norayr-noro/SUPPPAAAAAA_KEYBOARDDDD/SUPA_photos/bottomcase_(sketch).png

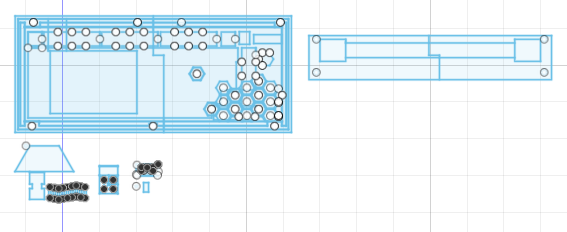
SUPA_photos/bottomcase_(sketch).png
