norayr-noro/SUPPPAAAAAA_KEYBOARDDDD/SUPA_photos/CAD_FULL.png

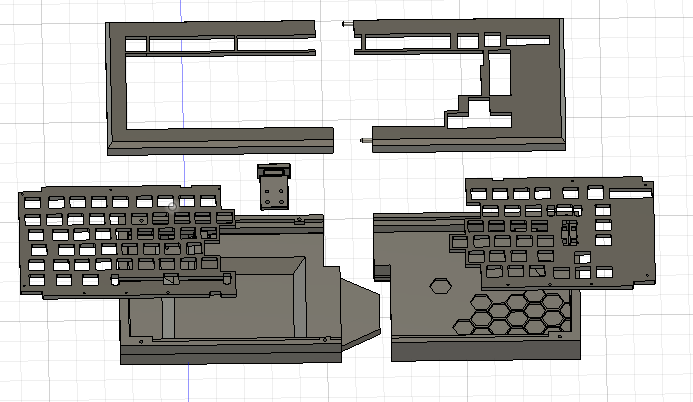
SUPA_photos/CAD_FULL.png
