norayr-noro/SUPPPAAAAAA_KEYBOARDDDD/SUPA_photos/PCB_full(diff.perc.).png

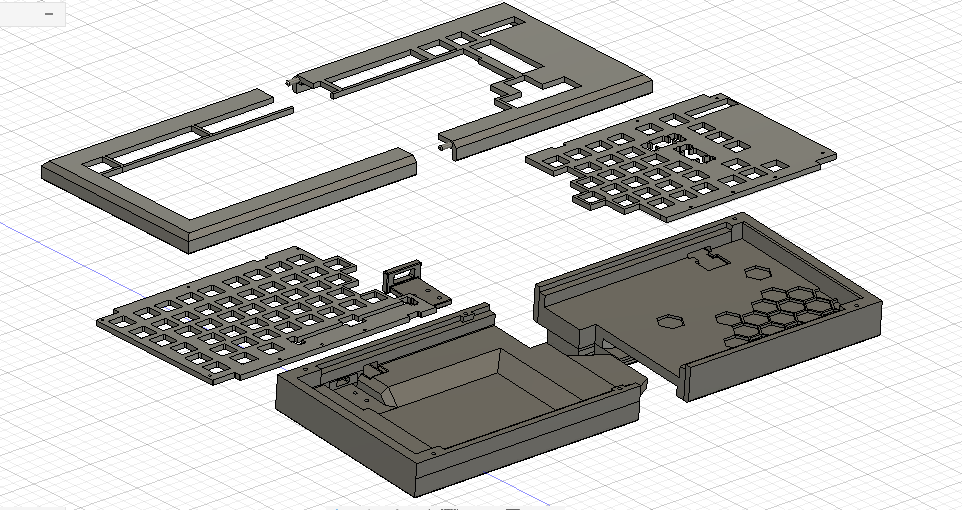
SUPA_photos/PCB_full(diff.perc.).png
