norayr-noro/SUPPPAAAAAA_KEYBOARDDDD/SUPA_photos/plate_(sketch).png

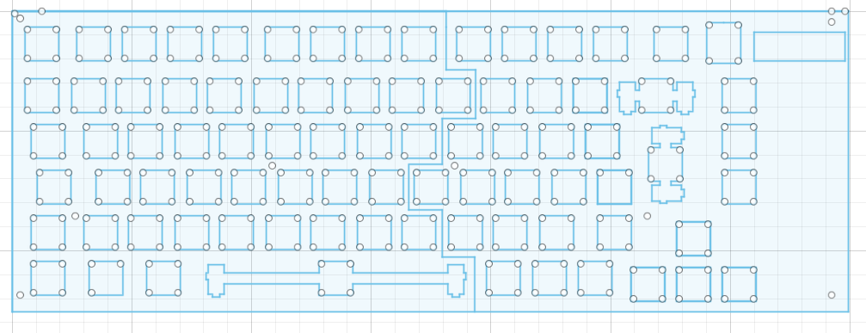
SUPA_photos/plate_(sketch).png
