norayr-noro/SUPPPAAAAAA_KEYBOARDDDD/SUPA_photos/Screenshot 2026-05-20 105105.png

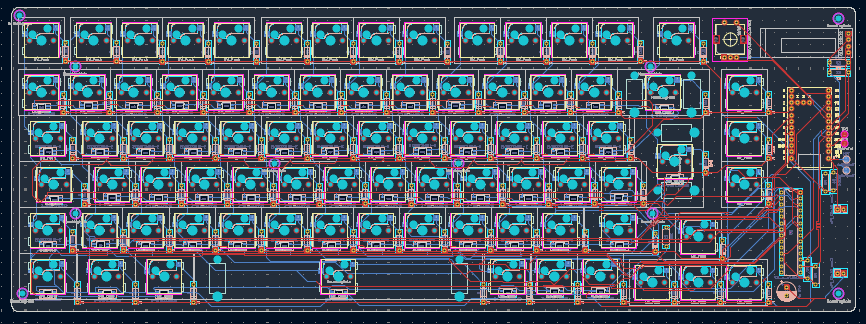
SUPA_photos/Screenshot 2026-05-20 105105.png
