norayr-noro/SUPPPAAAAAA_KEYBOARDDDD/SUPA_photos/Screenshot 2026-06-02 132246.png

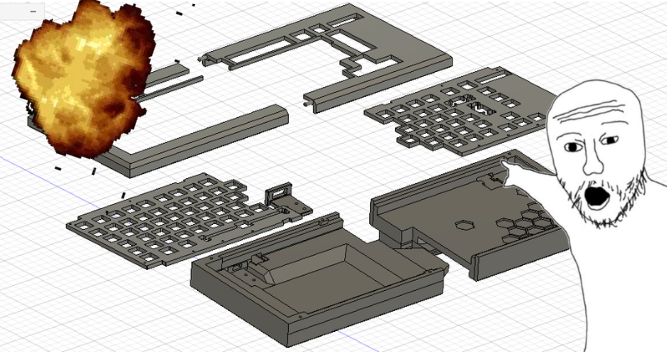
SUPA_photos/Screenshot 2026-06-02 132246.png
