norayr-noro/SUPPPAAAAAA_KEYBOARDDDD/SUPA_photos/topcase_(final).png

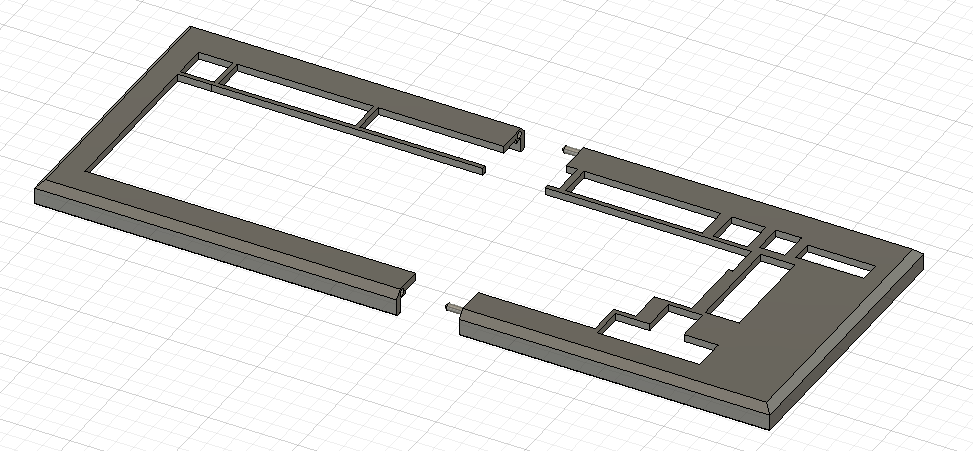
SUPA_photos/topcase_(final).png
