norayr-noro/SUPPPAAAAAA_KEYBOARDDDD/SUPA_photos/topcase_(sketch).png

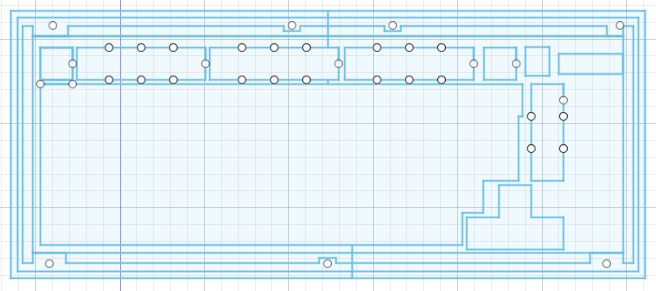
SUPA_photos/topcase_(sketch).png
