norayr-noro/SUPPPAAAAAA_KEYBOARDDDD/SUPA_photos/full_parts2.png

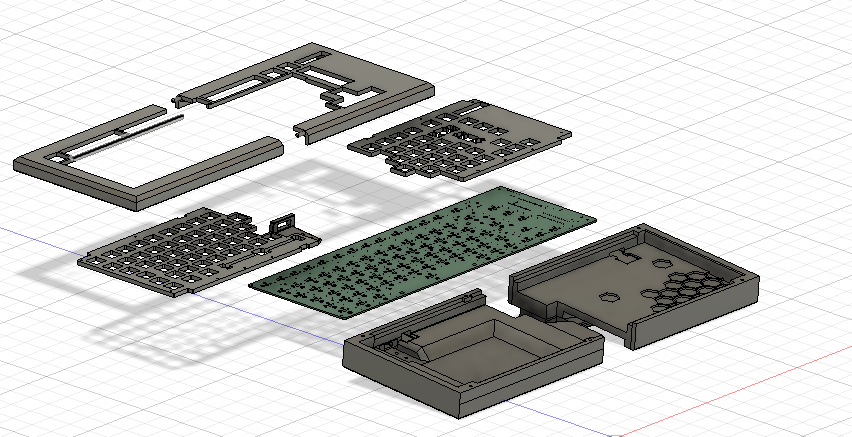
SUPA_photos/full_parts2.png
