norayr-noro/SUPPPAAAAAA_KEYBOARDDDD/SUPA_photos/full_parts.png

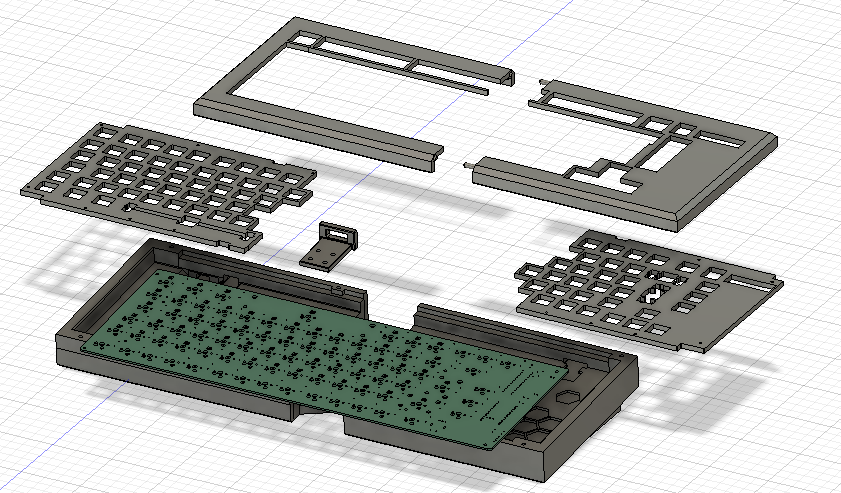
SUPA_photos/full_parts.png
