norayr-noro/SUPPPAAAAAA_KEYBOARDDDD/SUPA_photos/full_assembly2.png

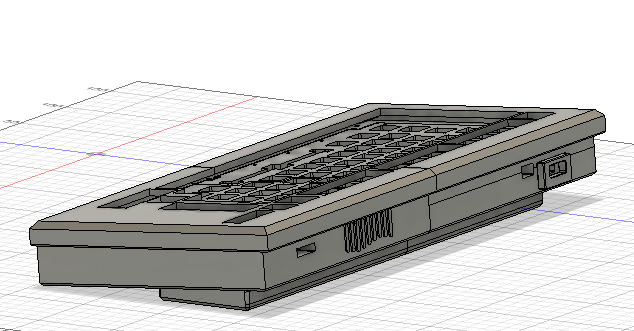
SUPA_photos/full_assembly2.png
