norayr-noro/SUPPPAAAAAA_KEYBOARDDDD/SUPA_photos/full_assembly.png

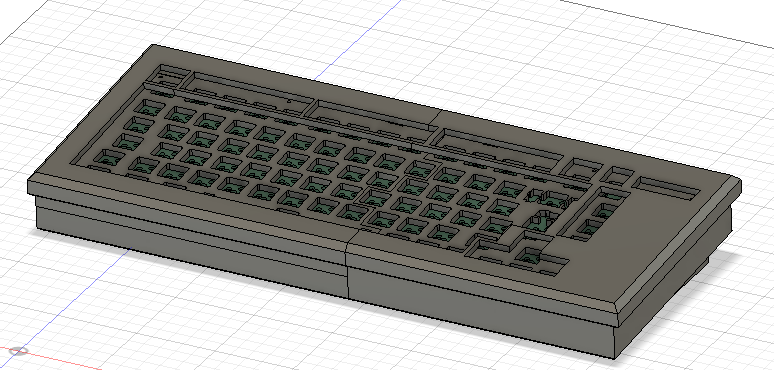
SUPA_photos/full_assembly.png
