norayr-noro/SUPPPAAAAAA_KEYBOARDDDD/SUPAAAA_KEYBOARD/SUPAAAA_KEYBOARD.kicad_sch

## KiCad design SUPAAAA_KEYBOARD/SUPAAAA_KEYBOARD.kicad_sch (2026-06-02)

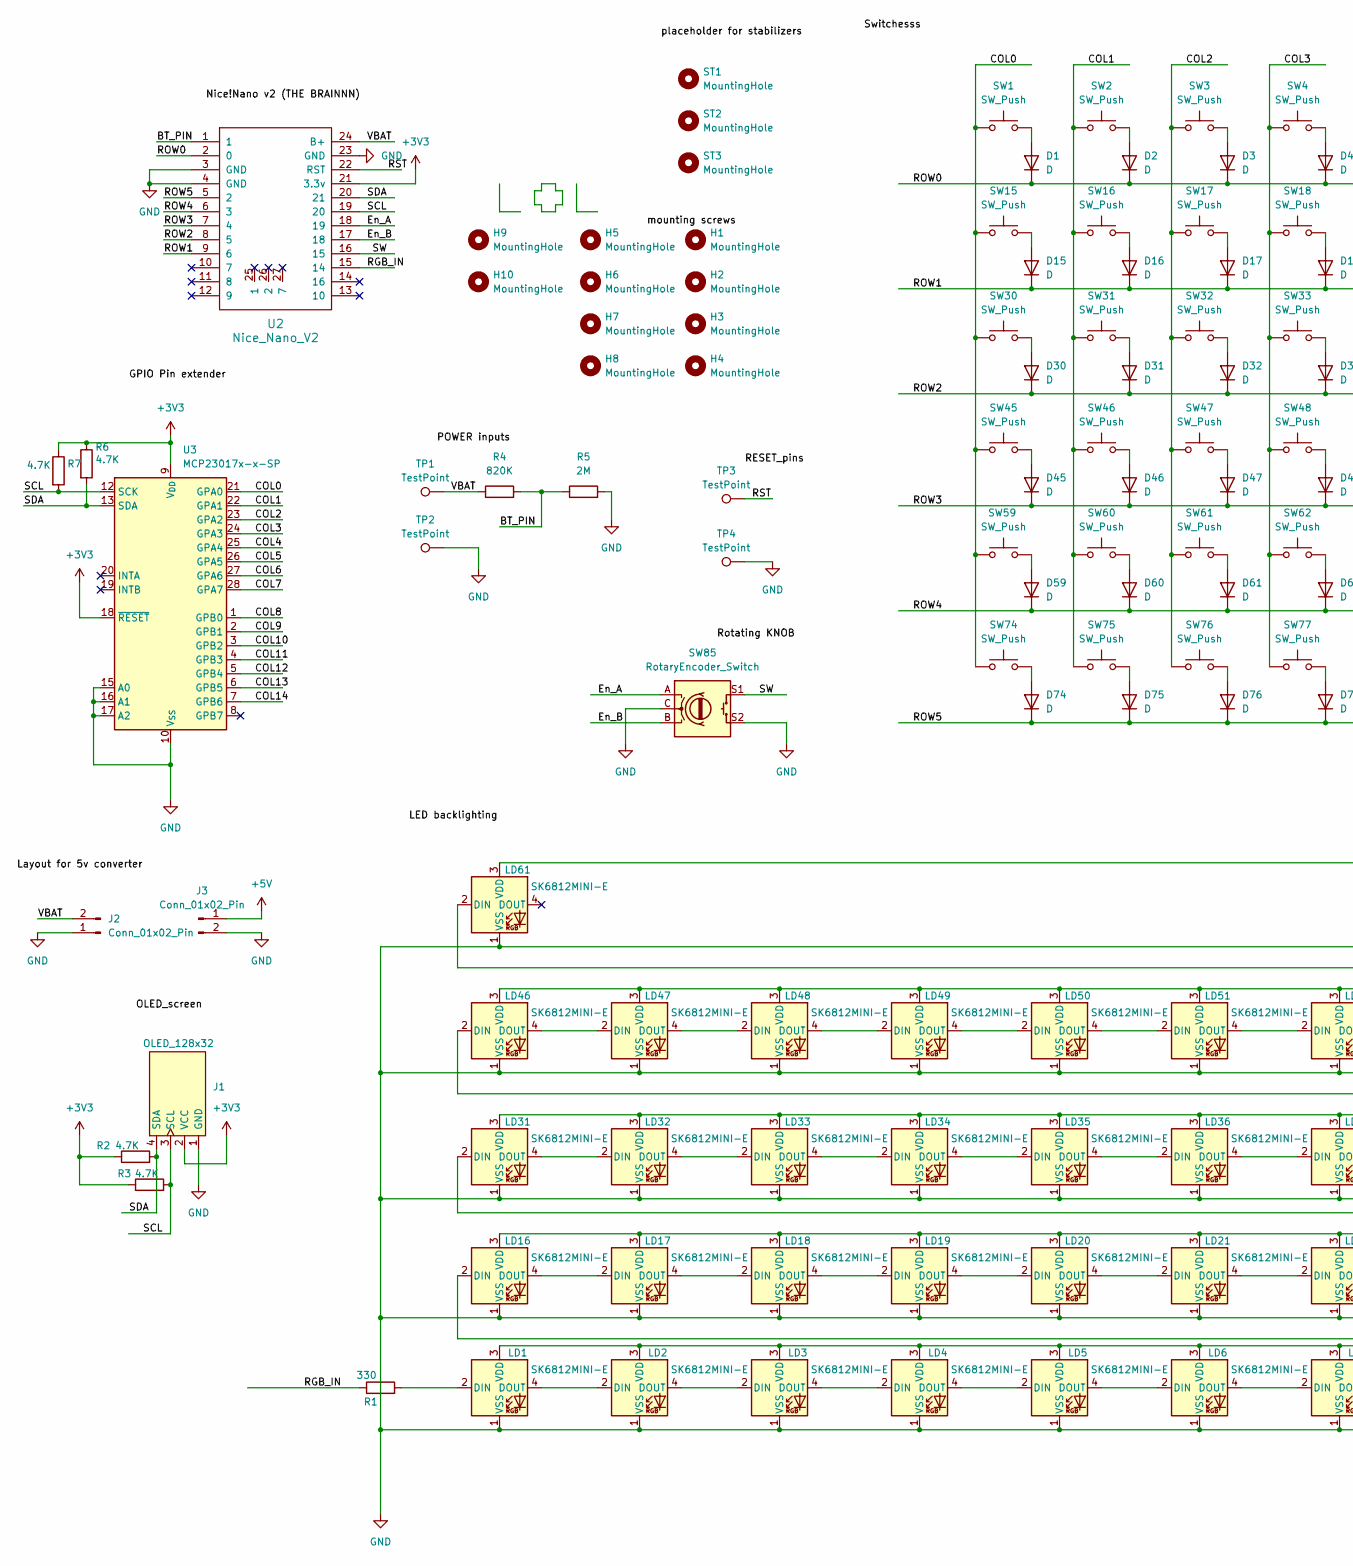
[picture p27: schematic SUPAAAA_KEYBOARD.kicad_sch, part in row 1, column 1]

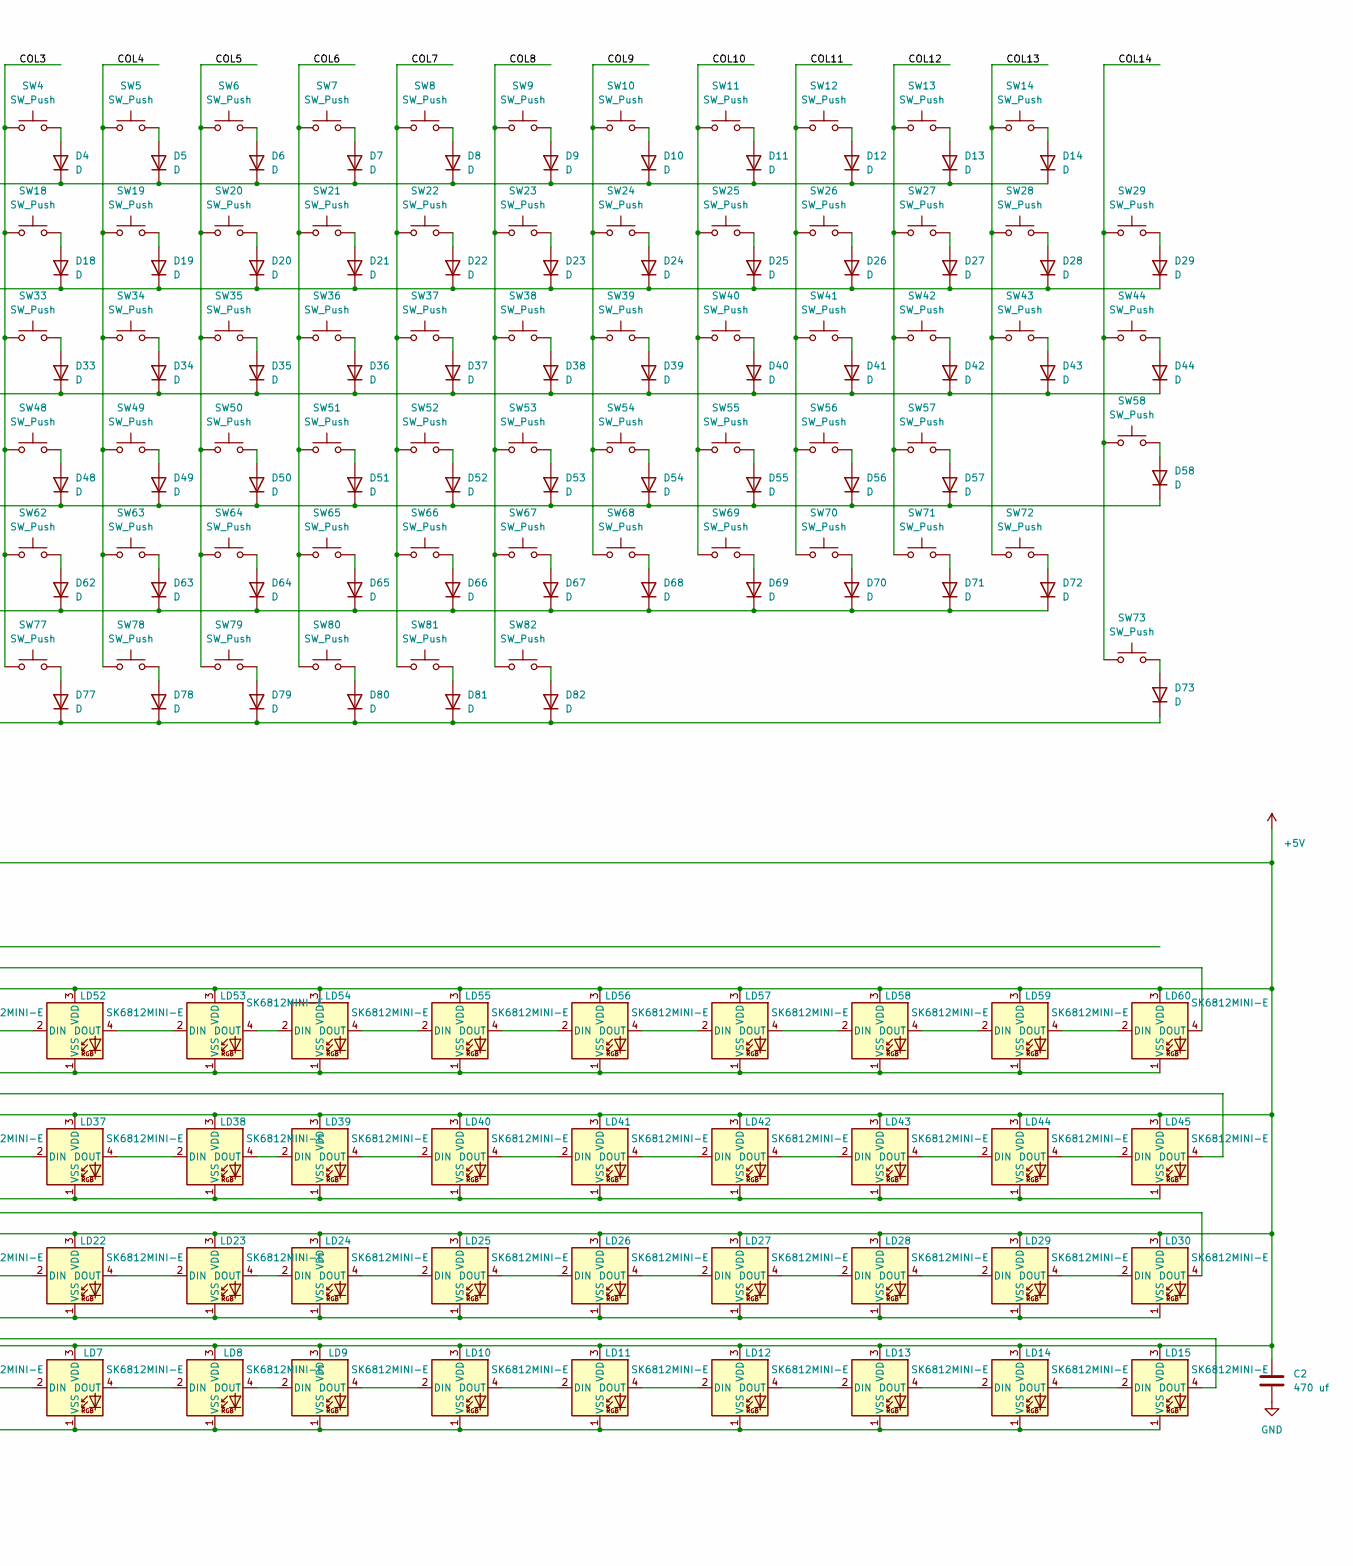
[picture p28: schematic SUPAAAA_KEYBOARD.kicad_sch, part in row 1, column 2]

Parts:
C2: 470 uf; CP_Radial_D8.0mm_P3.50mm
D1, D2, D3, D4, D5, D6, D7, D8, D9, D10, D11, D12, D13, D14, D15, D16, D17, D18, D19, D20, D21, D22, D23, D24, D25, D26, D27, D28, D29, D30, D31, D32, D33, D34, D35, D36, D37, D38, D39, D40, D41, D42, D43, D44, D45, D46, D47, D48, D49, D50, D51, D52, D53, D54, D55, D56, D57, D58, D59, D60, D61, D62, D63, D64, D65, D66, D67, D68, D69, D70, D71, D72, D73, D74, D75, D76, D77, D78, D79, D80, D81, D82: D; D_DO-35_SOD27_P7.62mm_Horizontal
H1, H2, H3, H4, H5, H6, H7, H8, H9, H10: MountingHole; MountingHole_2.2mm_M2
J1: OLED_128x32
J2, J3: Conn_01x02_Pin; PinHeader_1x02_P2.54mm_Vertical
LD1, LD2, LD3, LD4, LD5, LD6, LD7, LD8, LD9, LD10, LD11, LD12, LD13, LD14, LD15, LD16, LD17, LD18, LD19, LD20, LD21, LD22, LD23, LD24, LD25, LD26, LD27, LD28, LD29, LD30, LD31, LD32, LD33, LD34, LD35, LD36, LD37, LD38, LD39, LD40, LD41, LD42, LD43, LD44, LD45, LD46, LD47, LD48, LD49, LD50, LD51, LD52, LD53, LD54, LD55, LD56, LD57, LD58, LD59, LD60, LD61: SK6812MINI-E; LED_SK6812MINI-E_3.2x2.8mm_P1.5mm_ReverseMount
R1: 330; R_Axial_DIN0207_L6.3mm_D2.5mm_P7.62mm_Horizontal
R2, R3, R6, R7: 4.7K; R_Axial_DIN0207_L6.3mm_D2.5mm_P7.62mm_Horizontal
R4: 820K; R_Axial_DIN0207_L6.3mm_D2.5mm_P7.62mm_Horizontal
R5: 2M; R_Axial_DIN0207_L6.3mm_D2.5mm_P7.62mm_Horizontal
ST1: MountingHole; Stabilizer_MX_6.25u
ST2, ST3: MountingHole; Stabilizer_MX_2.00u
SW1, SW2, SW3, SW4, SW5, SW6, SW7, SW8, SW9, SW10, SW11, SW12, SW13, SW14, SW15, SW16, SW17, SW18, SW19, SW20, SW21, SW22, SW23, SW24, SW25, SW26, SW27, SW29, SW31, SW32, SW33, SW34, SW35, SW36, SW37, SW38, SW39, SW40, SW41, SW42, SW44, SW46, SW47, SW48, SW49, SW50, SW51, SW52, SW53, SW54, SW55, SW56, SW57, SW58, SW60, SW61, SW62, SW63, SW64, SW65, SW66, SW67, SW68, SW69, SW70, SW72, SW73, SW78, SW79, SW80, SW81, SW82: SW_Push; Hotswap_MX_1.00u
SW28: SW_Push; Hotswap_MX_2.00u
SW30, SW59, SW74, SW75, SW76: SW_Push; Hotswap_MX_1.25u
SW43: SW_Push; Hotswap_MX_ISOEnter
SW45, SW71: SW_Push; Hotswap_MX_1.50u
SW77: SW_Push; Hotswap_MX_6.25u
SW85: RotaryEncoder_Switch; RotaryEncoder_Alps_EC11E-Switch_Vertical_H20mm
TP1, TP2: TestPoint; TestPoint_Pad_D2.5mm
TP3, TP4: TestPoint; TestPoint_Pad_D2.0mm
U2: Nice_Nano_V2
U3: MCP23017x-x-SP; DIP-28_W7.62mm

Connections:
+3V3: J1.2 (VCC), R2.1, R3.1, R6.1, R7.1, U2.21 (3.3v), U3.9 (V_{DD}), U3.18 (~RESET)
+5V: C2.1, J3.1, LD1.3 (VDD), LD2.3 (VDD), LD3.3 (VDD), LD4.3 (VDD), LD5.3 (VDD), LD6.3 (VDD), LD7.3 (VDD), LD8.3 (VDD), LD9.3 (VDD), LD10.3 (VDD), LD11.3 (VDD), LD12.3 (VDD), LD13.3 (VDD), LD14.3 (VDD), LD15.3 (VDD), LD16.3 (VDD), LD17.3 (VDD), LD18.3 (VDD), LD19.3 (VDD), LD20.3 (VDD), LD21.3 (VDD), LD22.3 (VDD), LD23.3 (VDD), LD24.3 (VDD), LD25.3 (VDD), LD26.3 (VDD), LD27.3 (VDD), LD28.3 (VDD), LD29.3 (VDD), LD30.3 (VDD), LD31.3 (VDD), LD32.3 (VDD), LD33.3 (VDD), LD34.3 (VDD), LD35.3 (VDD), LD36.3 (VDD), LD37.3 (VDD), LD38.3 (VDD), LD39.3 (VDD), LD40.3 (VDD), LD41.3 (VDD), LD42.3 (VDD), LD43.3 (VDD), LD44.3 (VDD), LD45.3 (VDD), LD46.3 (VDD), LD47.3 (VDD), LD48.3 (VDD), LD49.3 (VDD), LD50.3 (VDD), LD51.3 (VDD), LD52.3 (VDD), LD53.3 (VDD), LD54.3 (VDD), LD55.3 (VDD), LD56.3 (VDD), LD57.3 (VDD), LD58.3 (VDD), LD59.3 (VDD), LD60.3 (VDD), LD61.3 (VDD)
BT_PIN: R4.2, R5.1, U2.1
COL0: SW1.1, SW15.1, SW30.1, SW45.1, SW59.1, SW74.1, U3.21 (GPA0)
COL1: SW2.1, SW16.1, SW31.1, SW46.1, SW60.1, SW75.1, U3.22 (GPA1)
COL2: SW3.1, SW17.1, SW32.1, SW47.1, SW61.1, SW76.1, U3.23 (GPA2)
COL3: SW4.1, SW18.1, SW33.1, SW48.1, SW62.1, SW77.1, U3.24 (GPA3)
COL4: SW5.1, SW19.1, SW34.1, SW49.1, SW63.1, SW78.1, U3.25 (GPA4)
COL5: SW6.1, SW20.1, SW35.1, SW50.1, SW64.1, SW79.1, U3.26 (GPA5)
COL6: SW7.1, SW21.1, SW36.1, SW51.1, SW65.1, SW80.1, U3.27 (GPA6)
COL7: SW8.1, SW22.1, SW37.1, SW52.1, SW66.1, SW81.1, U3.28 (GPA7)
COL8: SW9.1, SW23.1, SW38.1, SW53.1, SW67.1, SW82.1, U3.1 (GPB0)
COL9: SW10.1, SW24.1, SW39.1, SW54.1, SW68.1, U3.2 (GPB1)
COL10: SW11.1, SW25.1, SW40.1, SW55.1, SW69.1, U3.3 (GPB2)
COL11: SW12.1, SW26.1, SW41.1, SW56.1, SW70.1, U3.4 (GPB3)
COL12: SW13.1, SW27.1, SW42.1, SW57.1, SW71.1, U3.5 (GPB4)
COL13: SW14.1, SW28.1, SW43.1, SW72.1, U3.6 (GPB5)
COL14: SW29.1, SW44.1, SW58.1, SW73.1, U3.7 (GPB6)
En_A: SW85.A, U2.18 (19)
En_B: SW85.B, U2.17 (18)
GND: C2.2, J1.1 (GND), J2.1, J3.2, LD1.1 (VSS), LD2.1 (VSS), LD3.1 (VSS), LD4.1 (VSS), LD5.1 (VSS), LD6.1 (VSS), LD7.1 (VSS), LD8.1 (VSS), LD9.1 (VSS), LD10.1 (VSS), LD11.1 (VSS), LD12.1 (VSS), LD13.1 (VSS), LD14.1 (VSS), LD15.1 (VSS), LD16.1 (VSS), LD17.1 (VSS), LD18.1 (VSS), LD19.1 (VSS), LD20.1 (VSS), LD21.1 (VSS), LD22.1 (VSS), LD23.1 (VSS), LD24.1 (VSS), LD25.1 (VSS), LD26.1 (VSS), LD27.1 (VSS), LD28.1 (VSS), LD29.1 (VSS), LD30.1 (VSS), LD31.1 (VSS), LD32.1 (VSS), LD33.1 (VSS), LD34.1 (VSS), LD35.1 (VSS), LD36.1 (VSS), LD37.1 (VSS), LD38.1 (VSS), LD39.1 (VSS), LD40.1 (VSS), LD41.1 (VSS), LD42.1 (VSS), LD43.1 (VSS), LD44.1 (VSS), LD45.1 (VSS), LD46.1 (VSS), LD47.1 (VSS), LD48.1 (VSS), LD49.1 (VSS), LD50.1 (VSS), LD51.1 (VSS), LD52.1 (VSS), LD53.1 (VSS), LD54.1 (VSS), LD55.1 (VSS), LD56.1 (VSS), LD57.1 (VSS), LD58.1 (VSS), LD59.1 (VSS), LD60.1 (VSS), LD61.1 (VSS), R5.2, SW85.C, SW85.S2, TP2.1, TP4.1, U2.3 (GND), U2.4 (GND), U2.23 (GND), U3.10 (V_{SS}), U3.15 (A0), U3.16 (A1), U3.17 (A2)
unnamed: D1.2 (A), SW1.2
unnamed: D2.2 (A), SW2.2
unnamed: D3.2 (A), SW3.2
unnamed: D4.2 (A), SW4.2
unnamed: D5.2 (A), SW5.2
unnamed: D6.2 (A), SW6.2
unnamed: D7.2 (A), SW7.2
unnamed: D8.2 (A), SW8.2
unnamed: D9.2 (A), SW9.2
unnamed: D10.2 (A), SW10.2
unnamed: D11.2 (A), SW11.2
unnamed: D12.2 (A), SW12.2
unnamed: D13.2 (A), SW13.2
unnamed: D14.2 (A), SW14.2
unnamed: D15.2 (A), SW15.2
unnamed: D16.2 (A), SW16.2
unnamed: D17.2 (A), SW17.2
unnamed: D18.2 (A), SW18.2
unnamed: D19.2 (A), SW19.2
unnamed: D20.2 (A), SW20.2
unnamed: D21.2 (A), SW21.2
unnamed: D22.2 (A), SW22.2
unnamed: D23.2 (A), SW23.2
unnamed: D24.2 (A), SW24.2
unnamed: D25.2 (A), SW25.2
unnamed: D26.2 (A), SW26.2
unnamed: D27.2 (A), SW27.2
unnamed: D28.2 (A), SW28.2
unnamed: D29.2 (A), SW29.2
unnamed: D30.2 (A), SW30.2
unnamed: D31.2 (A), SW31.2
unnamed: D32.2 (A), SW32.2
unnamed: D33.2 (A), SW33.2
unnamed: D34.2 (A), SW34.2
unnamed: D35.2 (A), SW35.2
unnamed: D36.2 (A), SW36.2
unnamed: D37.2 (A), SW37.2
unnamed: D38.2 (A), SW38.2
unnamed: D39.2 (A), SW39.2
unnamed: D40.2 (A), SW40.2
unnamed: D41.2 (A), SW41.2
unnamed: D42.2 (A), SW42.2
unnamed: D43.2 (A), SW43.2
unnamed: D44.2 (A), SW44.2
unnamed: D45.2 (A), SW45.2
unnamed: D46.2 (A), SW46.2
unnamed: D47.2 (A), SW47.2
unnamed: D48.2 (A), SW48.2
unnamed: D49.2 (A), SW49.2
unnamed: D50.2 (A), SW50.2
unnamed: D51.2 (A), SW51.2
unnamed: D52.2 (A), SW52.2
unnamed: D53.2 (A), SW53.2
unnamed: D54.2 (A), SW54.2
unnamed: D55.2 (A), SW55.2
unnamed: D56.2 (A), SW56.2
unnamed: D57.2 (A), SW57.2
unnamed: D58.2 (A), SW58.2
unnamed: D59.2 (A), SW59.2
unnamed: D60.2 (A), SW60.2
unnamed: D61.2 (A), SW61.2
unnamed: D62.2 (A), SW62.2
unnamed: D63.2 (A), SW63.2
unnamed: D64.2 (A), SW64.2
unnamed: D65.2 (A), SW65.2
unnamed: D66.2 (A), SW66.2
unnamed: D67.2 (A), SW67.2
unnamed: D68.2 (A), SW68.2
unnamed: D69.2 (A), SW69.2
unnamed: D70.2 (A), SW70.2
unnamed: D71.2 (A), SW71.2
unnamed: D72.2 (A), SW72.2
unnamed: D73.2 (A), SW73.2
unnamed: D74.2 (A), SW74.2
unnamed: D75.2 (A), SW75.2
unnamed: D76.2 (A), SW76.2
unnamed: D77.2 (A), SW77.2
unnamed: D78.2 (A), SW78.2
unnamed: D79.2 (A), SW79.2
unnamed: D80.2 (A), SW80.2
unnamed: D81.2 (A), SW81.2
unnamed: D82.2 (A), SW82.2
unnamed: LD1.2 (DIN), R1.2
unnamed: LD1.4 (DOUT), LD2.2 (DIN)
unnamed: LD2.4 (DOUT), LD3.2 (DIN)
unnamed: LD3.4 (DOUT), LD4.2 (DIN)
unnamed: LD4.4 (DOUT), LD5.2 (DIN)
unnamed: LD5.4 (DOUT), LD6.2 (DIN)
unnamed: LD6.4 (DOUT), LD7.2 (DIN)
unnamed: LD7.4 (DOUT), LD8.2 (DIN)
unnamed: LD8.4 (DOUT), LD9.2 (DIN)
unnamed: LD9.4 (DOUT), LD10.2 (DIN)
unnamed: LD10.4 (DOUT), LD11.2 (DIN)
unnamed: LD11.4 (DOUT), LD12.2 (DIN)
unnamed: LD12.4 (DOUT), LD13.2 (DIN)
unnamed: LD13.4 (DOUT), LD14.2 (DIN)
unnamed: LD14.4 (DOUT), LD15.2 (DIN)
unnamed: LD15.4 (DOUT), LD16.2 (DIN)
unnamed: LD16.4 (DOUT), LD17.2 (DIN)
unnamed: LD17.4 (DOUT), LD18.2 (DIN)
unnamed: LD18.4 (DOUT), LD19.2 (DIN)
unnamed: LD19.4 (DOUT), LD20.2 (DIN)
unnamed: LD20.4 (DOUT), LD21.2 (DIN)
unnamed: LD21.4 (DOUT), LD22.2 (DIN)
unnamed: LD22.4 (DOUT), LD23.2 (DIN)
unnamed: LD23.4 (DOUT), LD24.2 (DIN)
unnamed: LD24.4 (DOUT), LD25.2 (DIN)
unnamed: LD25.4 (DOUT), LD26.2 (DIN)
unnamed: LD26.4 (DOUT), LD27.2 (DIN)
unnamed: LD27.4 (DOUT), LD28.2 (DIN)
unnamed: LD28.4 (DOUT), LD29.2 (DIN)
unnamed: LD29.4 (DOUT), LD30.2 (DIN)
unnamed: LD30.4 (DOUT), LD31.2 (DIN)
unnamed: LD31.4 (DOUT), LD32.2 (DIN)
unnamed: LD32.4 (DOUT), LD33.2 (DIN)
unnamed: LD33.4 (DOUT), LD34.2 (DIN)
unnamed: LD34.4 (DOUT), LD35.2 (DIN)
unnamed: LD35.4 (DOUT), LD36.2 (DIN)
unnamed: LD36.4 (DOUT), LD37.2 (DIN)
unnamed: LD37.4 (DOUT), LD38.2 (DIN)
unnamed: LD38.4 (DOUT), LD39.2 (DIN)
unnamed: LD39.4 (DOUT), LD40.2 (DIN)
unnamed: LD40.4 (DOUT), LD41.2 (DIN)
unnamed: LD41.4 (DOUT), LD42.2 (DIN)
unnamed: LD42.4 (DOUT), LD43.2 (DIN)
unnamed: LD43.4 (DOUT), LD44.2 (DIN)
unnamed: LD44.4 (DOUT), LD45.2 (DIN)
unnamed: LD45.4 (DOUT), LD46.2 (DIN)
unnamed: LD46.4 (DOUT), LD47.2 (DIN)
unnamed: LD47.4 (DOUT), LD48.2 (DIN)
unnamed: LD48.4 (DOUT), LD49.2 (DIN)
unnamed: LD49.4 (DOUT), LD50.2 (DIN)
unnamed: LD50.4 (DOUT), LD51.2 (DIN)
unnamed: LD51.4 (DOUT), LD52.2 (DIN)
unnamed: LD52.4 (DOUT), LD53.2 (DIN)
unnamed: LD53.4 (DOUT), LD54.2 (DIN)
unnamed: LD54.4 (DOUT), LD55.2 (DIN)
unnamed: LD55.4 (DOUT), LD56.2 (DIN)
unnamed: LD56.4 (DOUT), LD57.2 (DIN)
unnamed: LD57.4 (DOUT), LD58.2 (DIN)
unnamed: LD58.4 (DOUT), LD59.2 (DIN)
unnamed: LD59.4 (DOUT), LD60.2 (DIN)
unnamed: LD60.4 (DOUT), LD61.2 (DIN)
RGB_IN: R1.1, U2.15 (14)
ROW0: D1.1 (K), D2.1 (K), D3.1 (K), D4.1 (K), D5.1 (K), D6.1 (K), D7.1 (K), D8.1 (K), D9.1 (K), D10.1 (K), D11.1 (K), D12.1 (K), D13.1 (K), D14.1 (K), U2.2 (0)
ROW1: D15.1 (K), D16.1 (K), D17.1 (K), D18.1 (K), D19.1 (K), D20.1 (K), D21.1 (K), D22.1 (K), D23.1 (K), D24.1 (K), D25.1 (K), D26.1 (K), D27.1 (K), D28.1 (K), D29.1 (K), U2.9 (6)
ROW2: D30.1 (K), D31.1 (K), D32.1 (K), D33.1 (K), D34.1 (K), D35.1 (K), D36.1 (K), D37.1 (K), D38.1 (K), D39.1 (K), D40.1 (K), D41.1 (K), D42.1 (K), D43.1 (K), D44.1 (K), U2.8 (5)
ROW3: D45.1 (K), D46.1 (K), D47.1 (K), D48.1 (K), D49.1 (K), D50.1 (K), D51.1 (K), D52.1 (K), D53.1 (K), D54.1 (K), D55.1 (K), D56.1 (K), D57.1 (K), D58.1 (K), U2.7 (4)
ROW4: D59.1 (K), D60.1 (K), D61.1 (K), D62.1 (K), D63.1 (K), D64.1 (K), D65.1 (K), D66.1 (K), D67.1 (K), D68.1 (K), D69.1 (K), D70.1 (K), D71.1 (K), D72.1 (K), U2.6 (3)
ROW5: D73.1 (K), D74.1 (K), D75.1 (K), D76.1 (K), D77.1 (K), D78.1 (K), D79.1 (K), D80.1 (K), D81.1 (K), D82.1 (K), U2.5 (2)
RST: TP3.1, U2.22 (RST)
SCL: J1.3 (SCL), R3.2, R7.2, U2.19 (20), U3.12 (SCK)
SDA: J1.4 (SDA), R2.2, R6.2, U2.20 (21), U3.13 (SDA)
SW: SW85.S1, U2.16 (15)
VBAT: J2.2, R4.1, TP1.1, U2.24 (B+)
